Iona-401/Knight-Stick/mechanical/Grip/Grip - Right.step

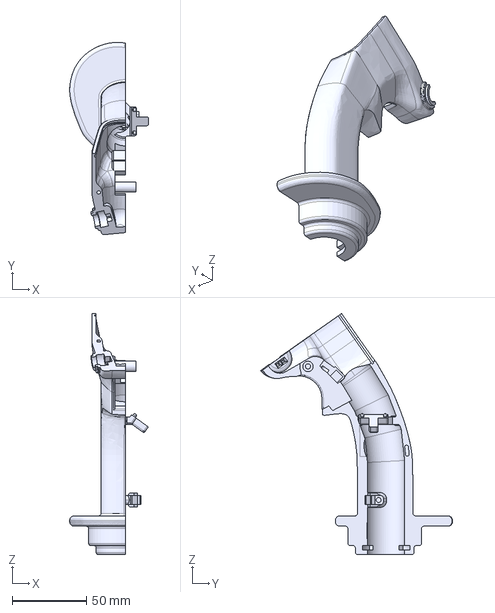
[picture p15: CAD file, 2026-03-21]
mechanical/Grip/Grip - Right.step
52.9 x 129.1 x 162.0 mm
