Iona-401/Knight-Stick/mechanical/X Axis/X Axis - Axis Damper.step

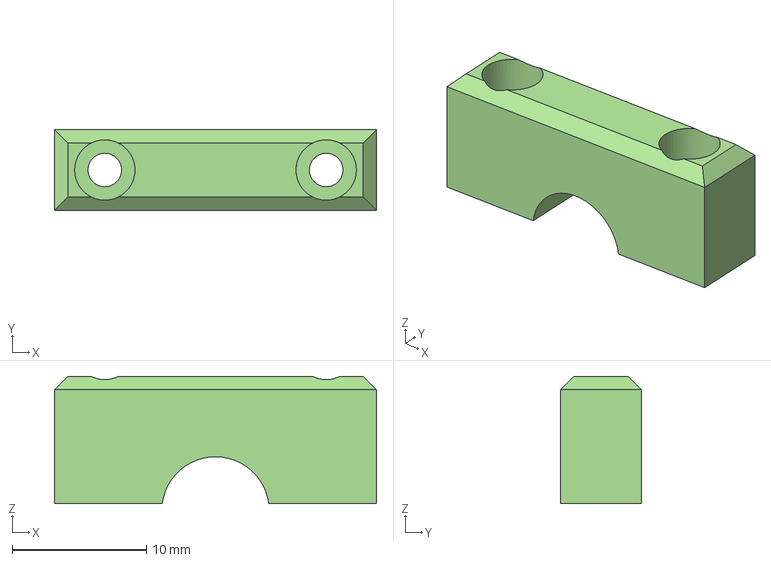
[picture p16: CAD file, 2026-03-21]
mechanical/X Axis/X Axis - Axis Damper.step
24.0 x 6.00 x 9.50 mm
