Iona-401/Knight-Stick/mechanical/Essentials/FS-Base.step

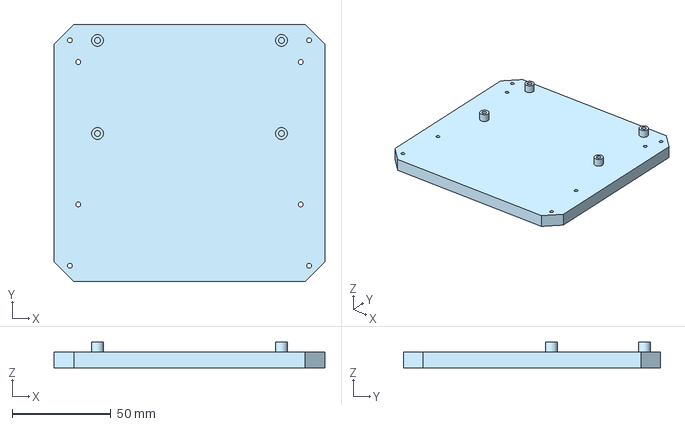
[picture p17: CAD file, 2026-03-21]
mechanical/Essentials/FS-Base.step
137.0 x 130.0 x 13.0 mm
