Iona-401/Knight-Stick/mechanical/Grip/Grip - Head Button Hat.step

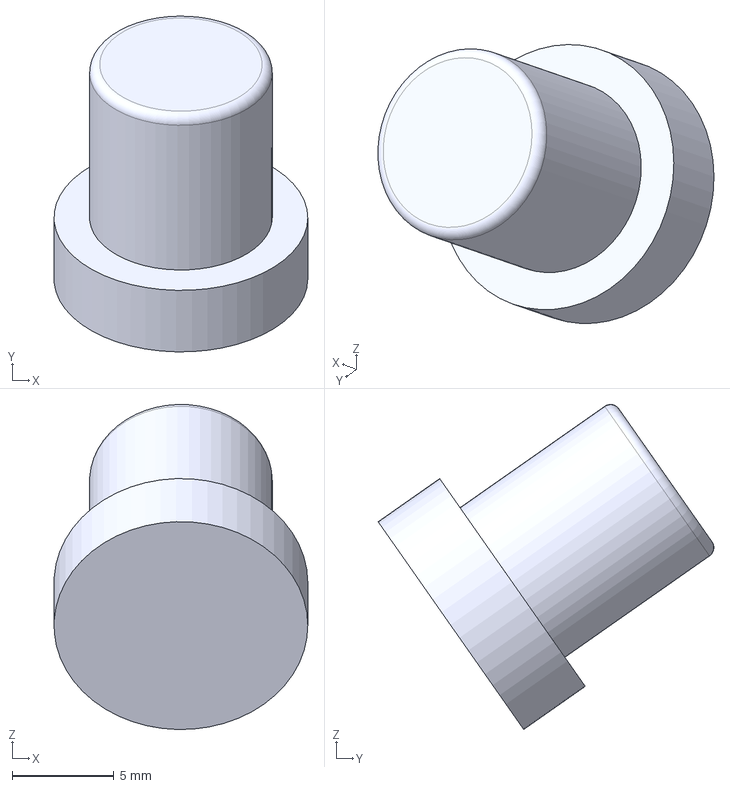
[picture p18: CAD file, 2026-03-21]
mechanical/Grip/Grip - Head Button Hat.step
12.5 x 16.5 x 16.0 mm
