Iona-401/Knight-Stick/mechanical/X Axis/X Axis - Grip Connector.step

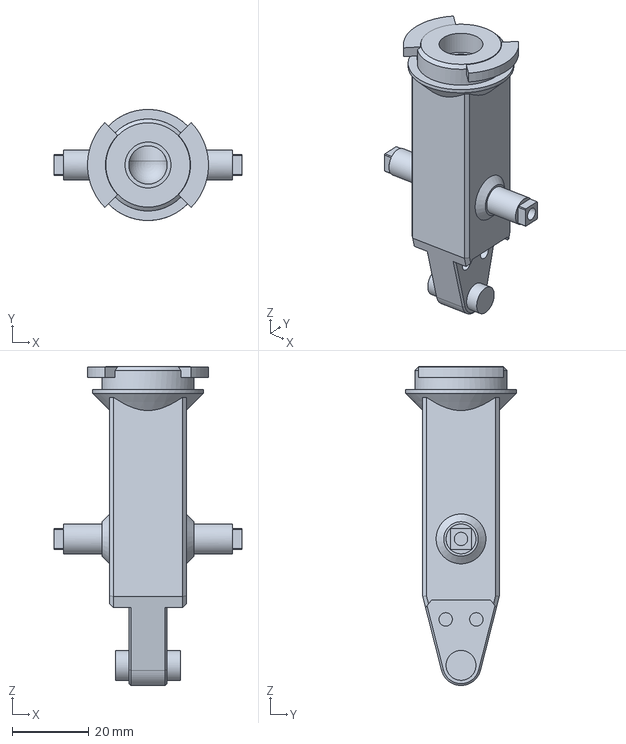
[picture p19: CAD file, 2026-03-21]
mechanical/X Axis/X Axis - Grip Connector.step
49.0 x 29.0 x 83.2 mm
