Iona-401/Knight-Stick/mechanical/Grip/Grip - Dome Hat.step

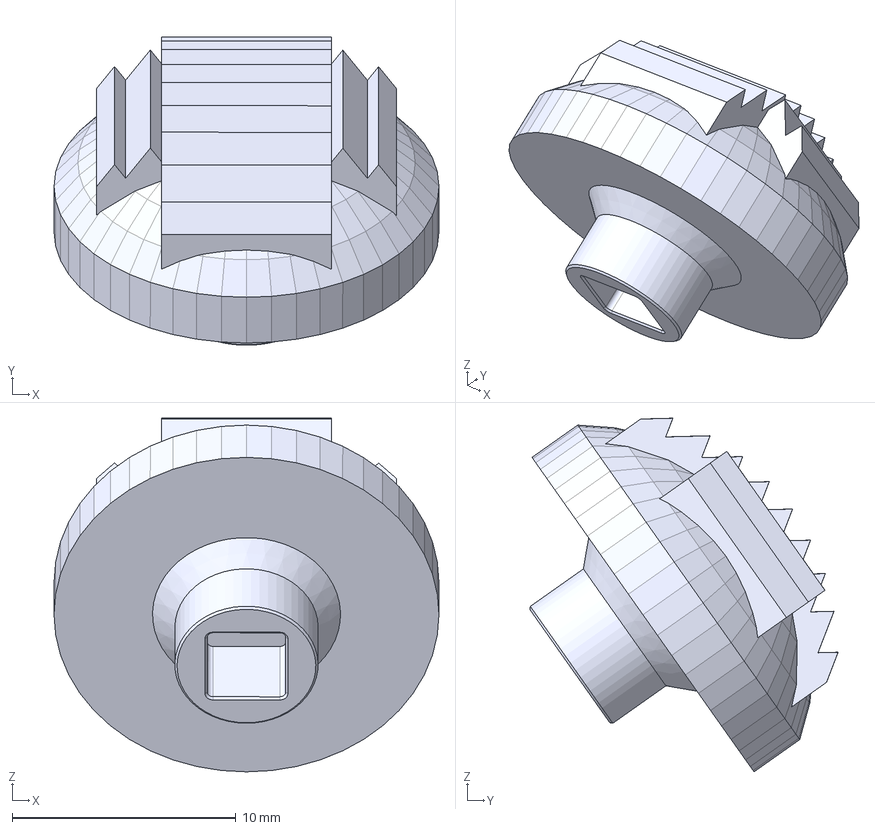
[picture p20: CAD file, 2026-03-21]
mechanical/Grip/Grip - Dome Hat.step
17.2 x 13.8 x 15.8 mm
