Iona-401/Knight-Stick/mechanical/X Axis/X Axis - Roller Cover.step

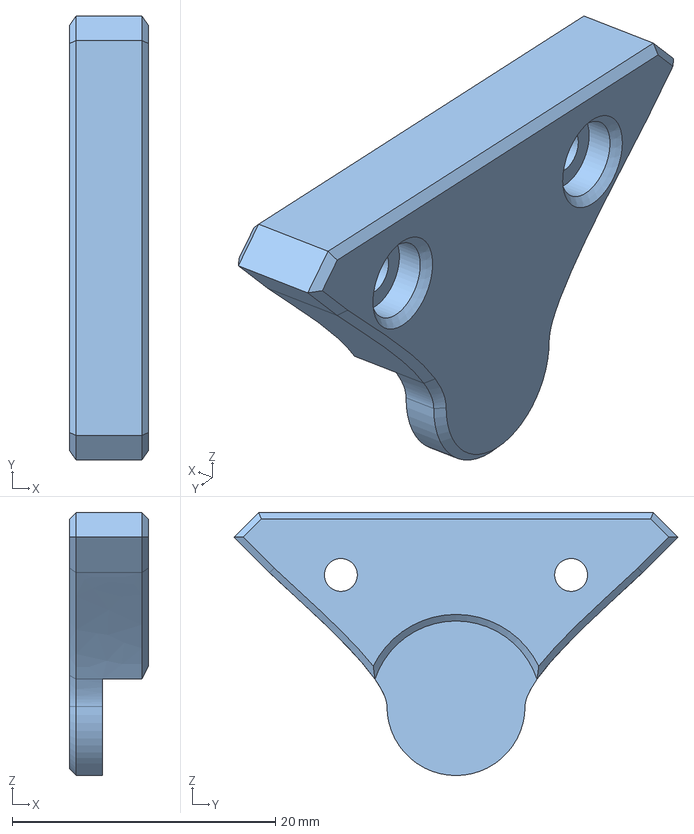
[picture p21: CAD file, 2026-03-21]
mechanical/X Axis/X Axis - Roller Cover.step
6.00 x 33.8 x 20.0 mm
