Iona-401/Knight-Stick/mechanical/Grip/Grip - Tact Button Cover.step

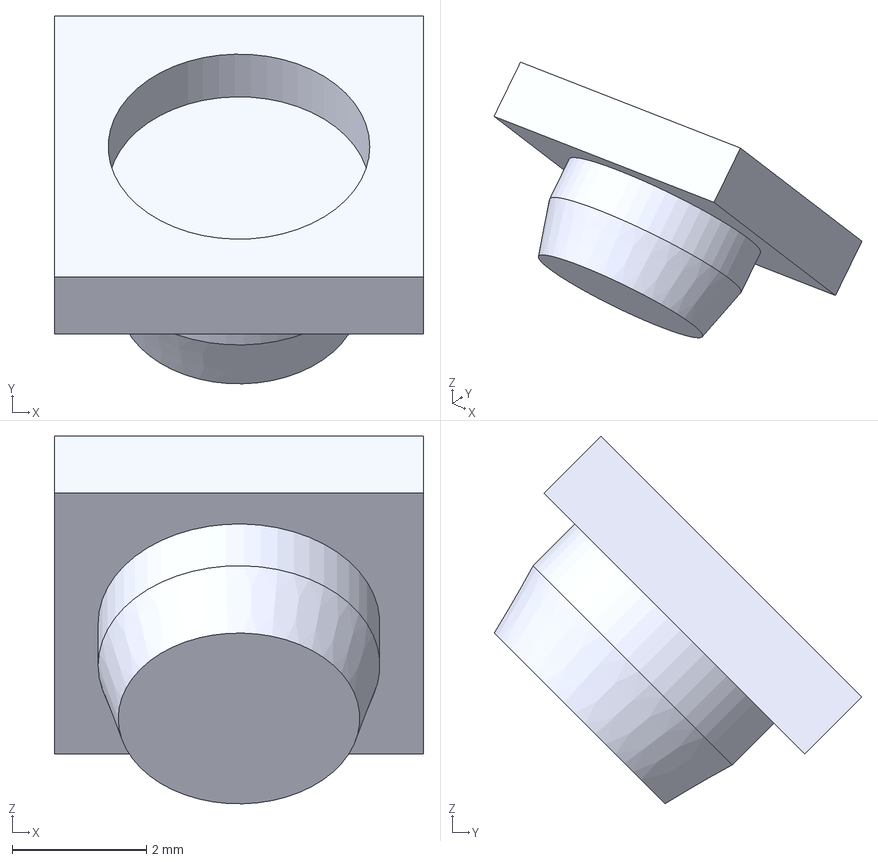
[picture p22: CAD file, 2026-03-21]
mechanical/Grip/Grip - Tact Button Cover.step
5.50 x 5.48 x 5.48 mm
