Iona-401/Knight-Stick/mechanical/X Axis/X Axis - Grip Roller Cover.step

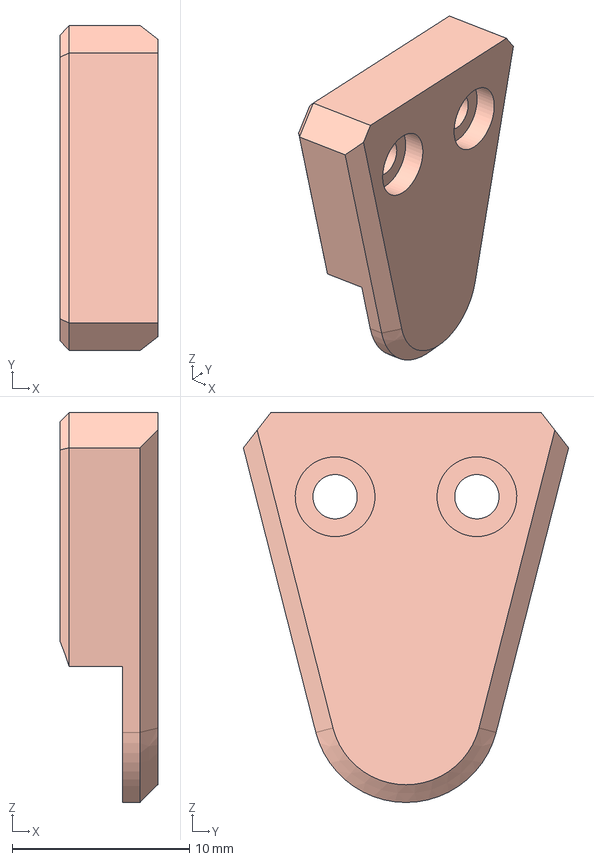
[picture p23: CAD file, 2026-03-21]
mechanical/X Axis/X Axis - Grip Roller Cover.step
5.50 x 18.3 x 22.0 mm
