Iona-401/Knight-Stick/mechanical/Grip/Grip - Trigger.step

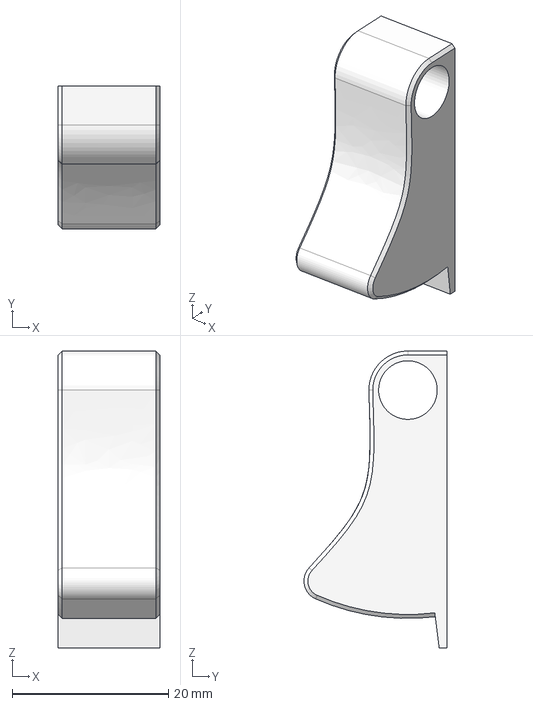
[picture p24: CAD file, 2026-03-21]
mechanical/Grip/Grip - Trigger.step
13.0 x 18.3 x 38.0 mm
