Iona-401/Knight-Stick/mechanical/Grip/Grip - Dimple Hat.step

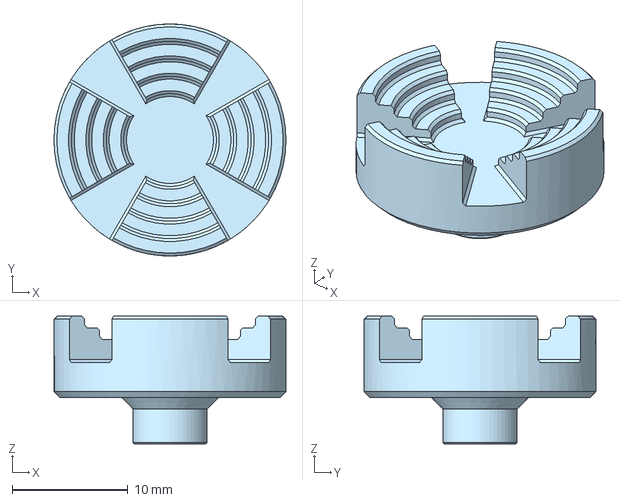
[picture p25: CAD file, 2026-03-21]
mechanical/Grip/Grip - Dimple Hat.step
20.0 x 20.0 x 11.0 mm
