Iona-401/Knight-Stick/mechanical/Grip/Grip - Head.step

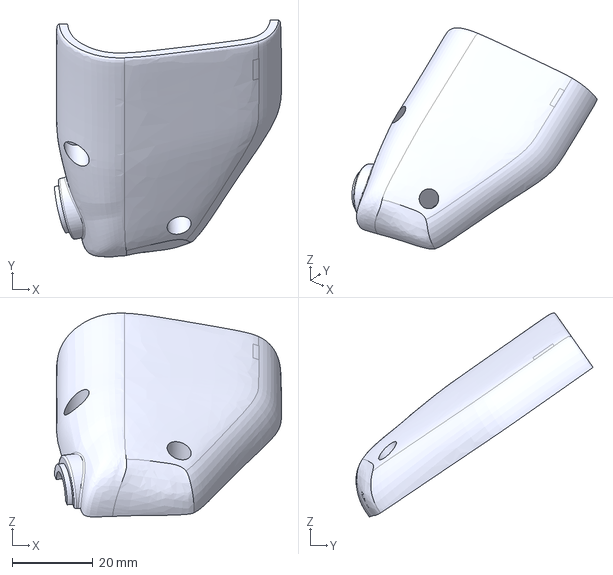
[picture p26: CAD file, 2026-03-21]
mechanical/Grip/Grip - Head.step
56.4 x 58.9 x 50.6 mm
