Iona-401/Knight-Stick/mechanical/Grip/Grip - Base Button Hat.step

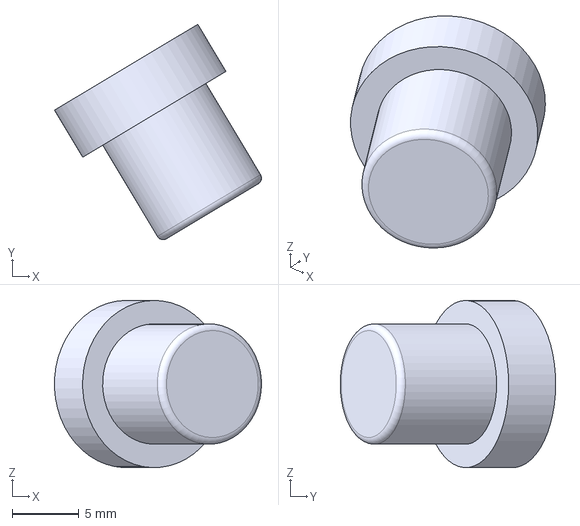
[picture p27: CAD file, 2026-03-21]
mechanical/Grip/Grip - Base Button Hat.step
15.5 x 16.1 x 12.5 mm
