Iona-401/Knight-Stick/mechanical/Grip/Grip - Face Plate.step

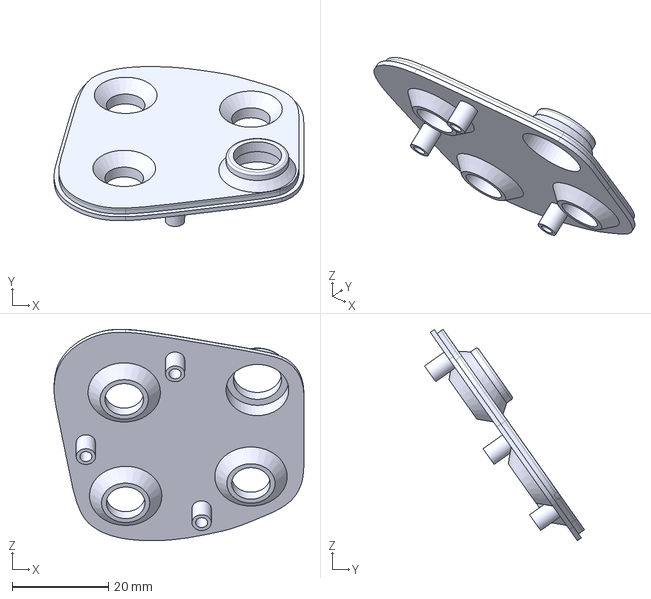
[picture p28: CAD file, 2026-03-21]
mechanical/Grip/Grip - Face Plate.step
51.8 x 33.2 x 43.8 mm
