Iona-401/Knight-Stick/mechanical/Grip/Grip - Left.step

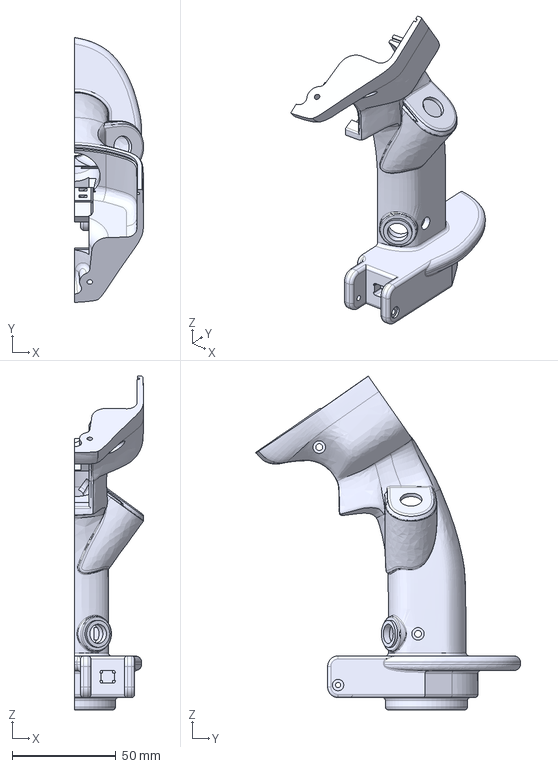
[picture p29: CAD file, 2026-03-21]
mechanical/Grip/Grip - Left.step
33.4 x 127.5 x 160.7 mm
