Iona-401/Knight-Stick/mechanical/Grip/Grip - Face Button Hat.step

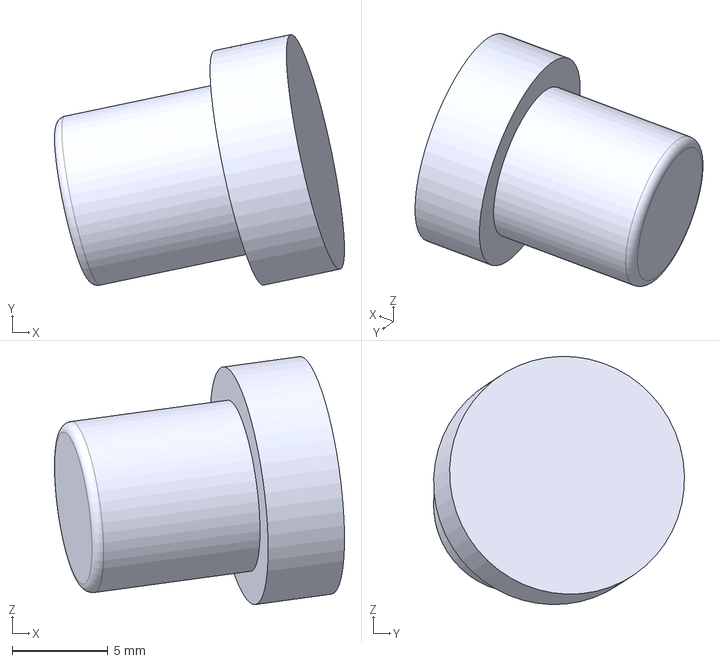
[picture p30: CAD file, 2026-03-21]
mechanical/Grip/Grip - Face Button Hat.step
15.1 x 13.1 x 12.9 mm
